sparkfun/SparkFun_Spectral_UV_Sensor_AS7331/site/assets/img/23518-Spectral-UV-Sensor-Feature.jpg

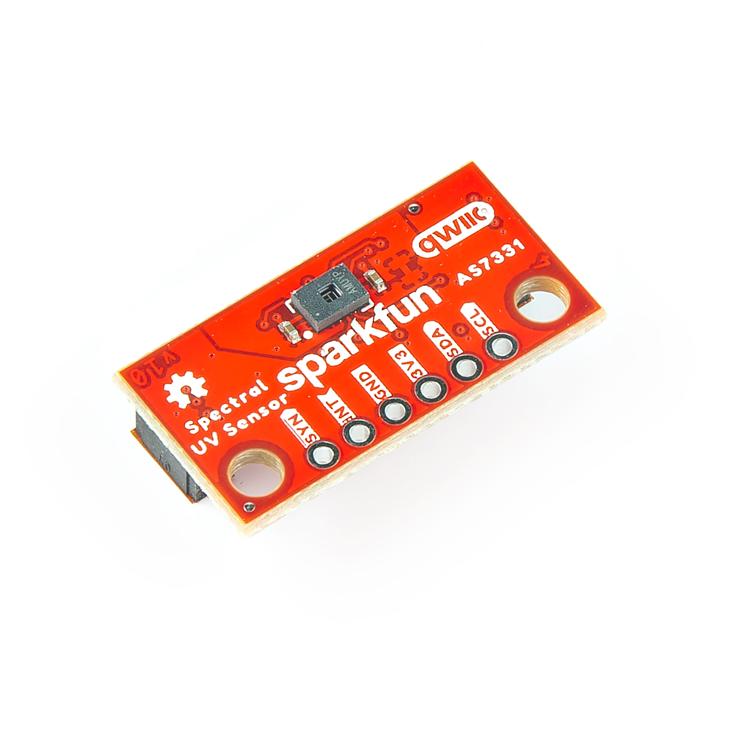
site/assets/img/23518-Spectral-UV-Sensor-Feature.jpg
